johngarrett/digital-light-meter/demo images/apt prio.jpg

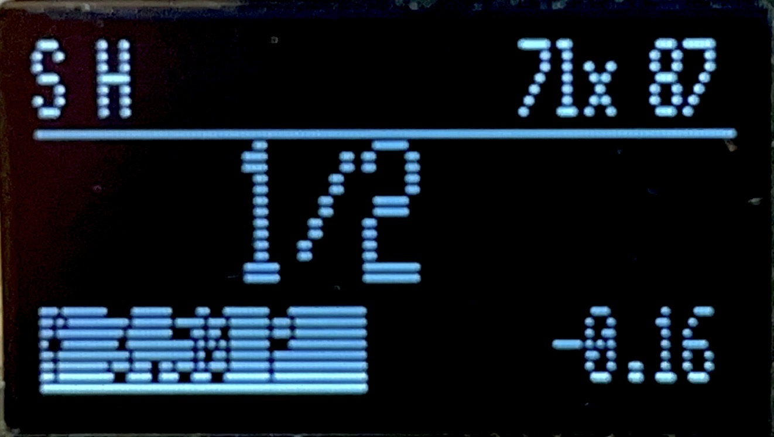
demo images/apt prio.jpg
