johngarrett/digital-light-meter/demo images/glamour shots/DSC02748.JPG

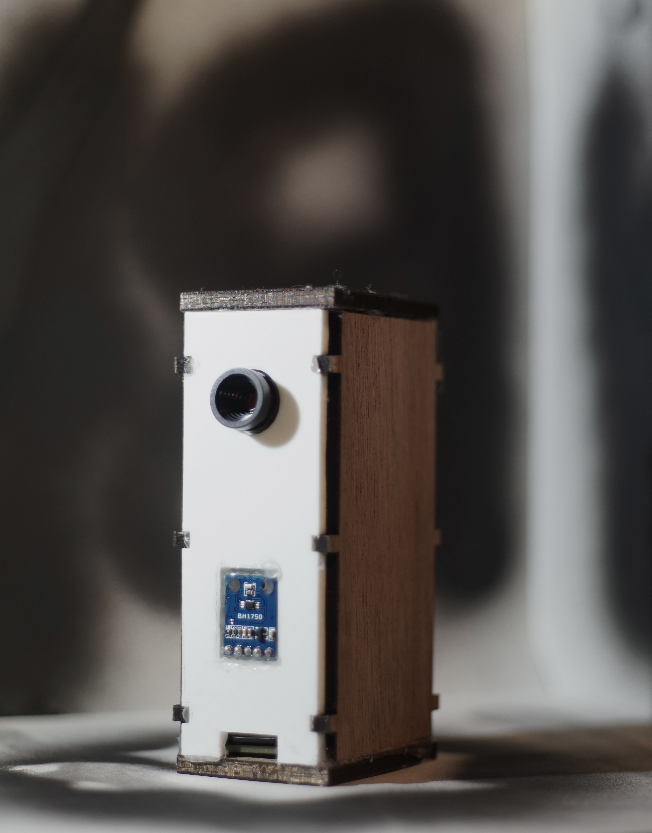
demo images/glamour shots/DSC02748.JPG
