johngarrett/digital-light-meter/demo images/glamour shots/DSC02755.JPG

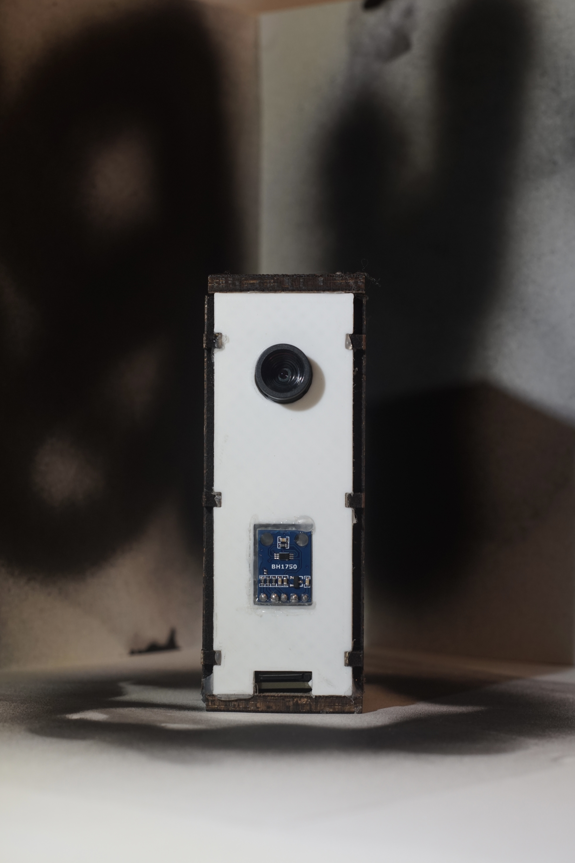
demo images/glamour shots/DSC02755.JPG
