johngarrett/digital-light-meter/demo images/glamour shots/DSC02761.JPG

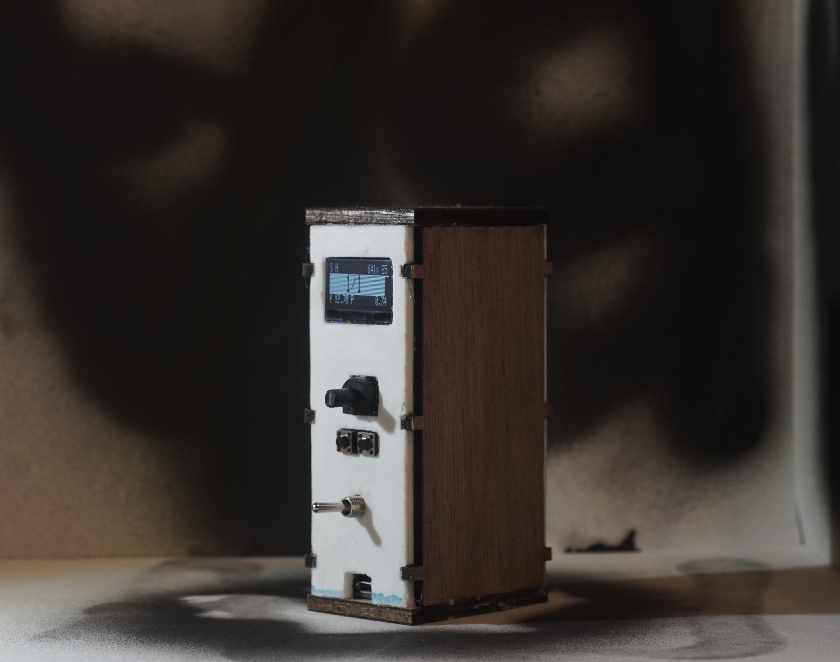
demo images/glamour shots/DSC02761.JPG
