johngarrett/digital-light-meter/demo images/glamour shots/DSC02774.JPG

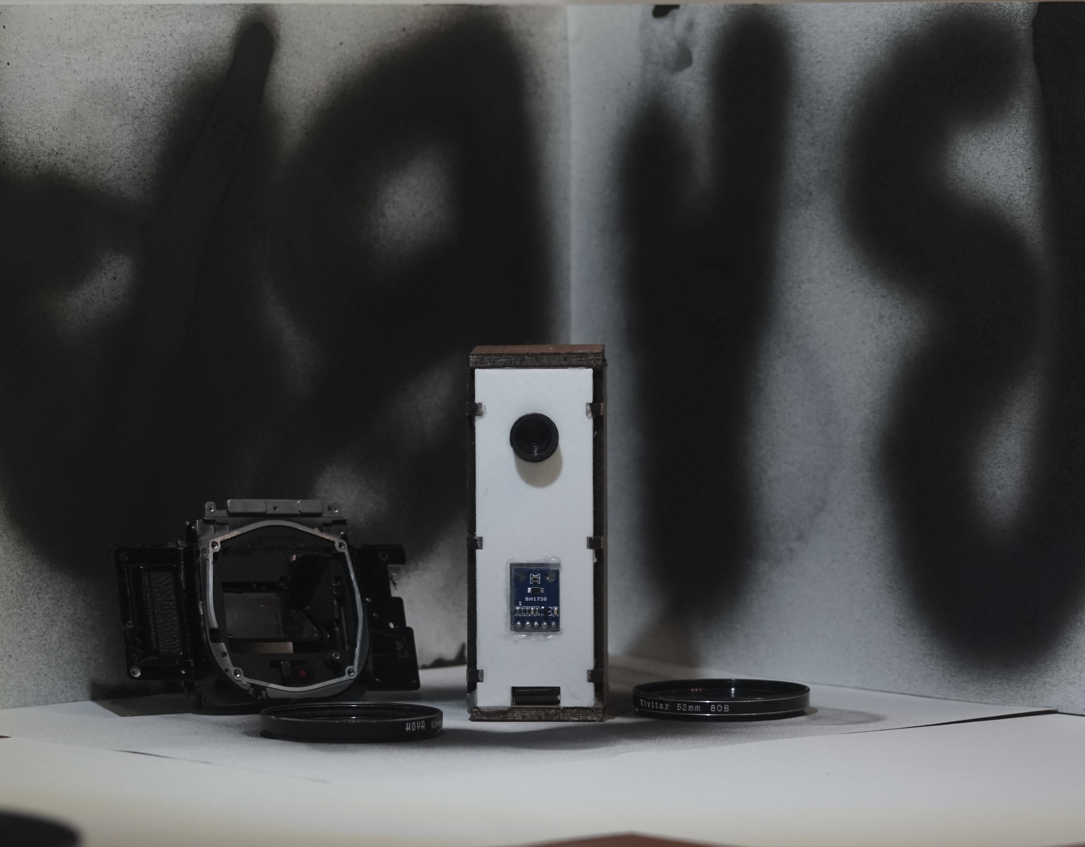
demo images/glamour shots/DSC02774.JPG
