johngarrett/digital-light-meter/demo images/glamour shots/DSC02786.JPG

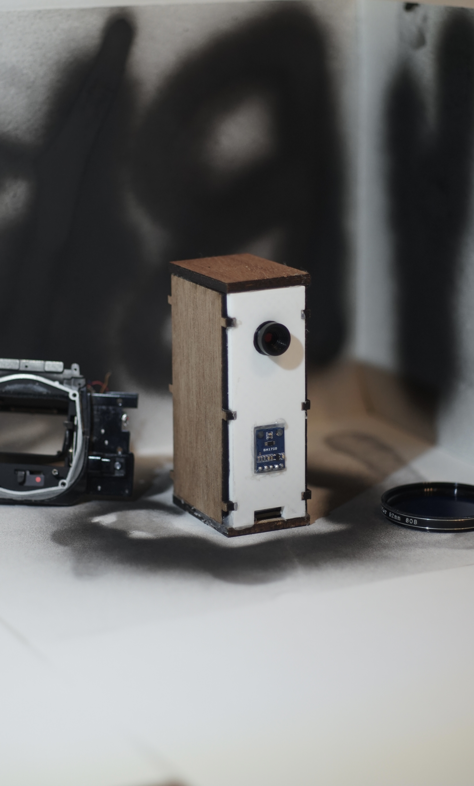
demo images/glamour shots/DSC02786.JPG
