johngarrett/digital-light-meter/demo images/glamour shots/DSC02799.JPG

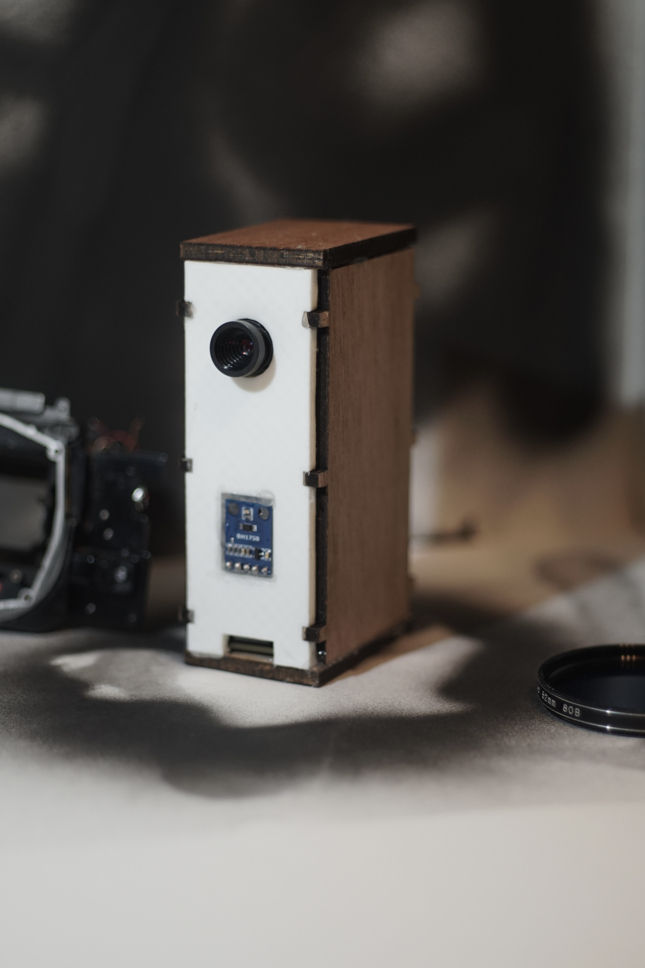
demo images/glamour shots/DSC02799.JPG
