johngarrett/digital-light-meter/film example/sd backup/0.JPG

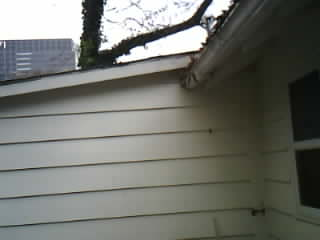
film example/sd backup/0.JPG
