johngarrett/digital-light-meter/film example/sd backup/1.JPG

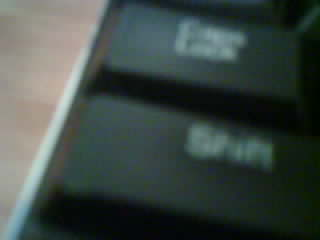
film example/sd backup/1.JPG
