johngarrett/digital-light-meter/film example/sd backup/24.JPG

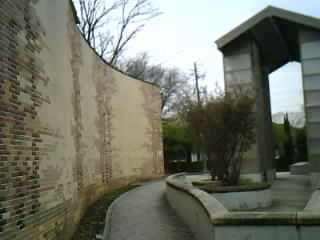
film example/sd backup/24.JPG
