johngarrett/digital-light-meter/film example/sd backup/25.JPG

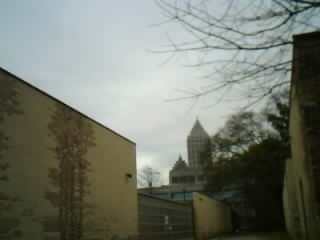
film example/sd backup/25.JPG
