johngarrett/digital-light-meter/film example/sd backup/26.JPG

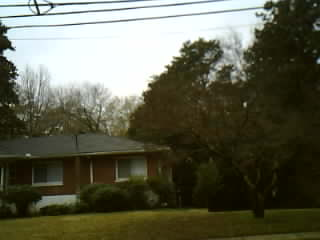
film example/sd backup/26.JPG
