johngarrett/digital-light-meter/film example/sd backup/27.JPG

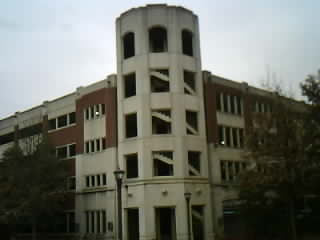
film example/sd backup/27.JPG
