johngarrett/digital-light-meter/film example/sd backup/28.JPG

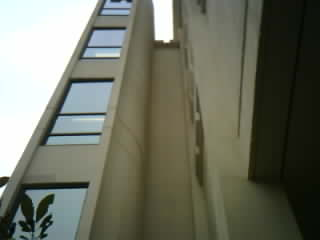
film example/sd backup/28.JPG
