johngarrett/digital-light-meter/film example/sd backup/29.JPG

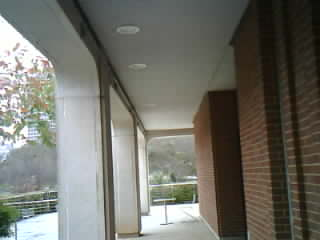
film example/sd backup/29.JPG
