johngarrett/digital-light-meter/film example/sd backup/30.JPG

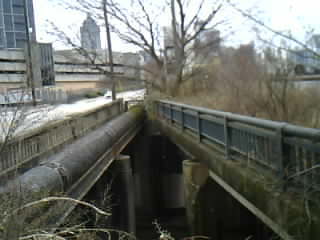
film example/sd backup/30.JPG
