johngarrett/digital-light-meter/film example/sd backup/31.JPG

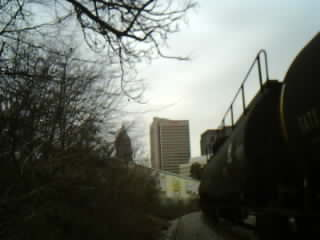
film example/sd backup/31.JPG
