johngarrett/digital-light-meter/film example/sd backup/32.JPG

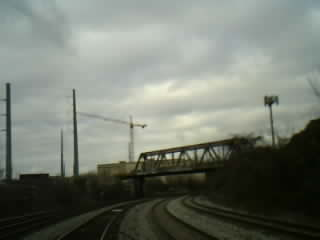
film example/sd backup/32.JPG
