johngarrett/digital-light-meter/film example/sd backup/33.JPG

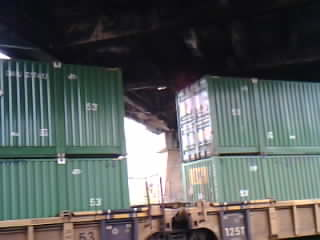
film example/sd backup/33.JPG
