johngarrett/digital-light-meter/film example/sd backup/36.JPG

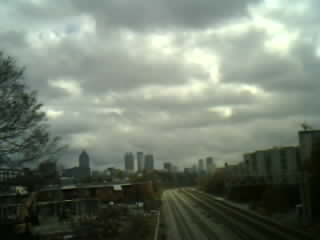
film example/sd backup/36.JPG
