johngarrett/digital-light-meter/digital_test/0.JPG

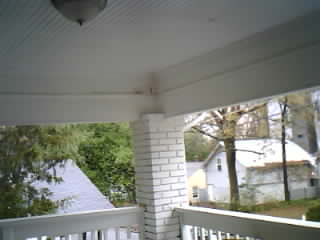
digital_test/0.JPG
