johngarrett/digital-light-meter/digital_test/1.JPG

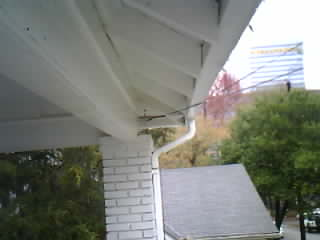
digital_test/1.JPG
