johngarrett/digital-light-meter/digital_test/2.JPG

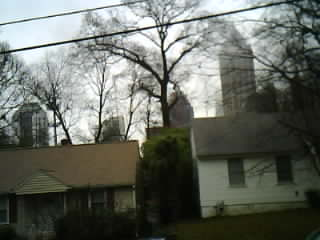
digital_test/2.JPG
