johngarrett/digital-light-meter/digital_test/3.JPG

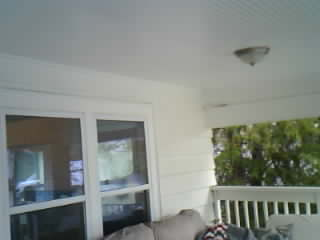
digital_test/3.JPG
