johngarrett/digital-light-meter/digital_test/4.JPG

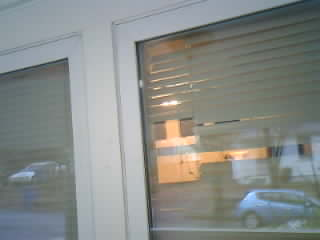
digital_test/4.JPG
